kelu124/0xa5eded/firmware/v2 firmware/adc/adc.h

//!
//! \file       adc.h
//! \author     Abdelrahman Ali
//! \date       2024-09-08
//!
//! \brief      adc pio.
//!

#ifndef ADC_H
#define ADC_H

//---------------------------------------------------------------------------
// INCLUDES
//---------------------------------------------------------------------------

#include <stdio.h>
#include <stdlib.h>
#include "pico/stdlib.h"
#include "hardware/pio.h"
#include "hardware/dma.h"
#include "hardware/clocks.h"

//---------------------------------------------------------------------------
// CONSTANTS
//---------------------------------------------------------------------------

#define PIN_BASE 0
#define PIN_BASE_CLK 28
#define SAMPLE_COUNT 8000
// #define SAMPLE_COUNT_TRG 4000
#define ADC_CLK 60000000

//---------------------------------------------------------------------------
// ADC INIT FUNCTION
//---------------------------------------------------------------------------

void pio_adc_init();

//---------------------------------------------------------------------------
// ADC DMA FUNCTION
//---------------------------------------------------------------------------

void pio_adc_dma();

//---------------------------------------------------------------------------
// ADC PREPARE SAMPLES FUNCTION
//---------------------------------------------------------------------------

void pio_adc_prepare_samples(uint16_t *samples);

//---------------------------------------------------------------------------
// ADC CLEAN FIFO FUNCTION
//---------------------------------------------------------------------------

void pio_adc_clear_fifos();

//---------------------------------------------------------------------------
// ADC MAIN FUNCTION
//---------------------------------------------------------------------------

void adc_trigger();

//---------------------------------------------------------------------------
// END OF FILE
//---------------------------------------------------------------------------

#endif
