kelu124/0xa5eded/firmware/v2 firmware/i2c/i2c.h

//!
//! \file       i2c.h
//! \author     Abdelrahman Ali
//! \date       2024-09-08
//!
//! \brief      i2c function.
//!

#ifndef I2C_H
#define I2C_H

//---------------------------------------------------------------------------
// INCLUDES
//---------------------------------------------------------------------------

#include <stdio.h>
#include <stdlib.h>
#include "pico/stdlib.h"
#include "pico/binary_info.h"
#include "hardware/i2c.h"
#include "hardware/gpio.h"
#include "hardware/clocks.h"

//---------------------------------------------------------------------------
// CONSTANTS
//---------------------------------------------------------------------------

#define I2C_PORT i2c1
#define I2C_SDA_PIN 18
#define I2C_SCL_PIN 19
#define GPIO20 20
#define I2C_FREQUENCY 100000

#define DEVICE_ADDRESS 0x2E

//---------------------------------------------------------------------------
// I2C INIT FUNCTION
//---------------------------------------------------------------------------
void pio_i2c_init();

//---------------------------------------------------------------------------
// I2C WRITE FUNCTION
//---------------------------------------------------------------------------
void pio_i2c_write(uint8_t data);

//---------------------------------------------------------------------------
// I2C MAIN FUNCTION
//---------------------------------------------------------------------------
void i2c_trigger();

//---------------------------------------------------------------------------
// END OF FILE
//---------------------------------------------------------------------------

#endif
